cristiandeda/TSC_E-BookReader/Images/img1.png

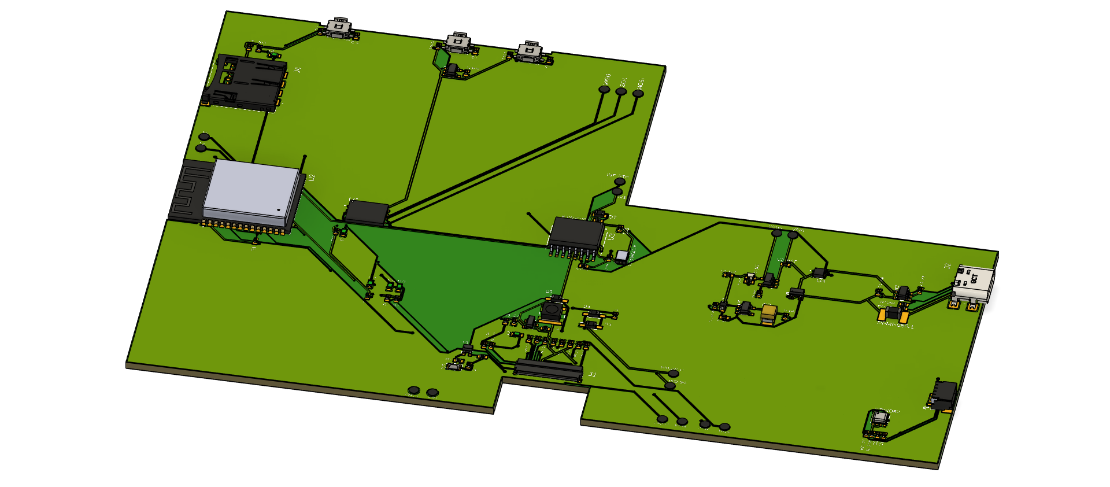
Images/img1.png
