cristiandeda/TSC_E-BookReader/Images/img2.png

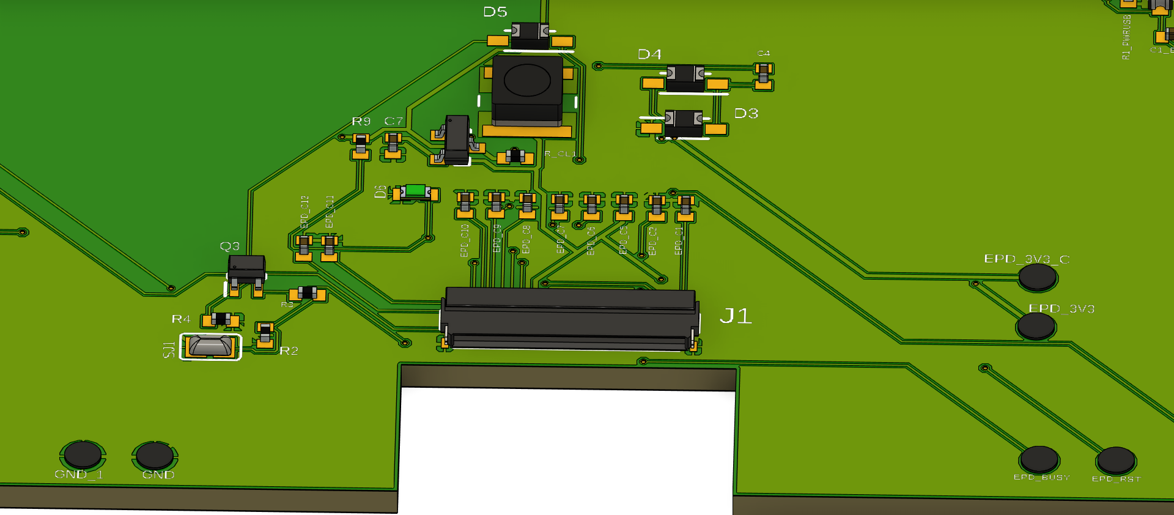
Images/img2.png
