cristiandeda/TSC_E-BookReader/Images/img3.png

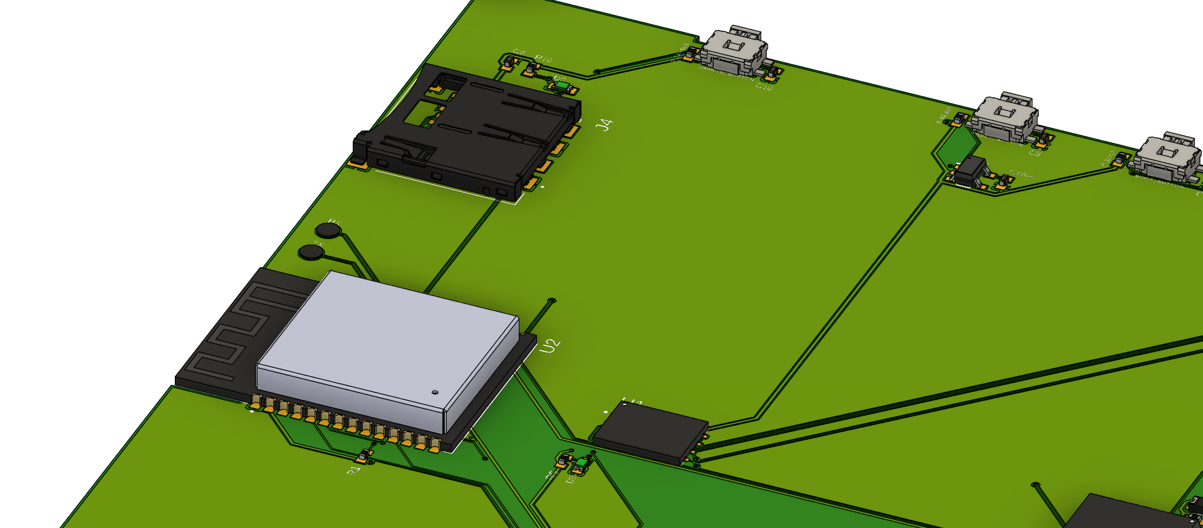
Images/img3.png
