cristiandeda/TSC_E-BookReader/Images/img4.png

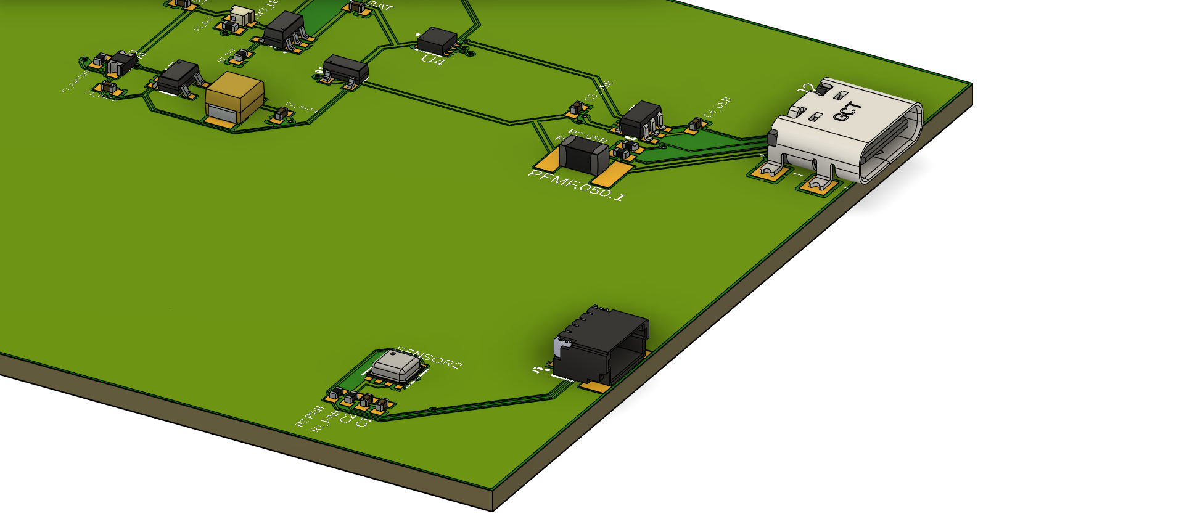
Images/img4.png
