cristiandeda/TSC_E-BookReader/Images/img5.png

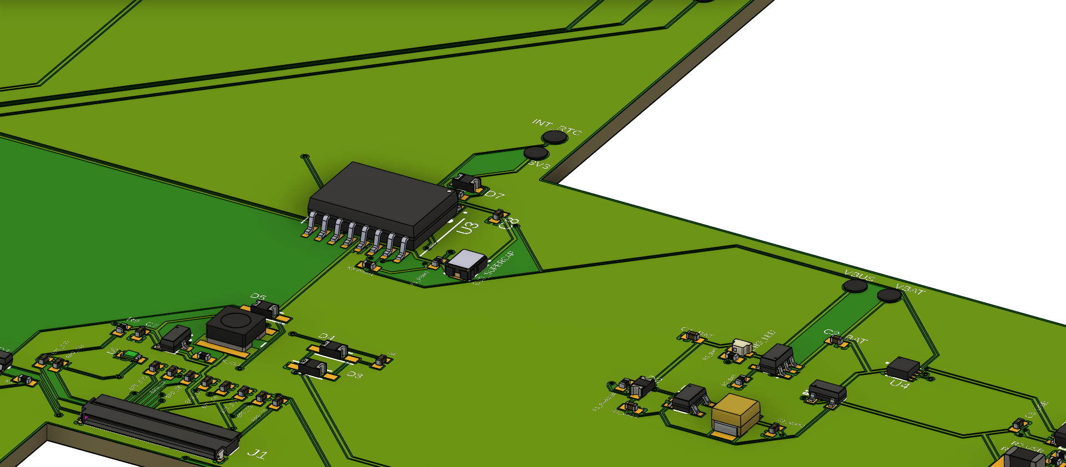
Images/img5.png
